sparkfun/SparkFun_Particulate_Matter_Sensor_Breakout_BMV080/docs/assets/img/BMV080_Breakout_Board_Secure.jpg

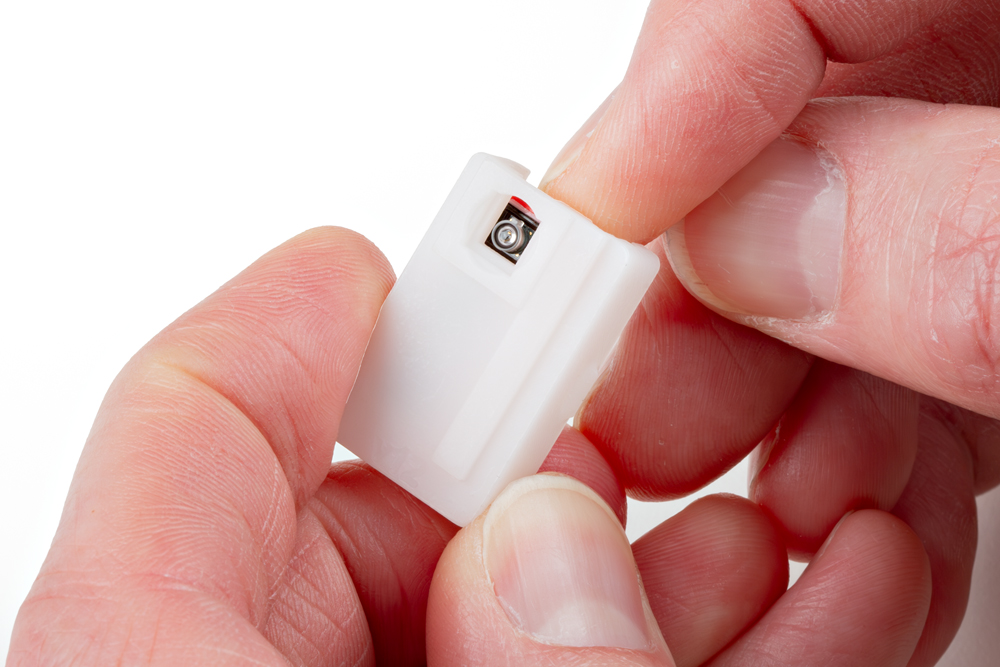
docs/assets/img/BMV080_Breakout_Board_Secure.jpg
