sparkfun/SparkFun_Particulate_Matter_Sensor_Breakout_BMV080/Enclosure/Demo_Mounting_Board/ESP32_ThingPlus_C_Dimensional_Mounting_001 (Meshed).stl

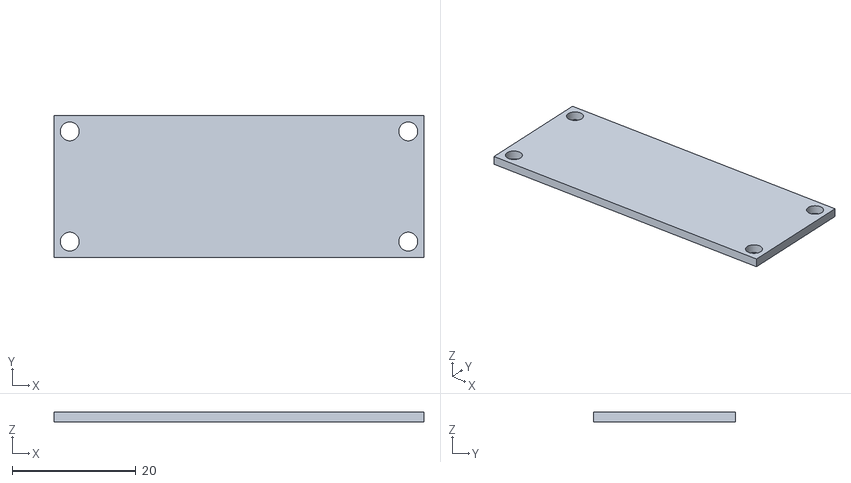
[picture p25: CAD file, 2024-12-12]
Enclosure/Demo_Mounting_Board/ESP32_ThingPlus_C_Dimensional_Mounting_001 (Meshed).stl
59.7 x 22.9 x 1.60
