sparkfun/SparkFun_Particulate_Matter_Sensor_Breakout_BMV080/Enclosure/Demo_Mounting_Board/HMV080_Demo_Mounting_Board_v02.dxf

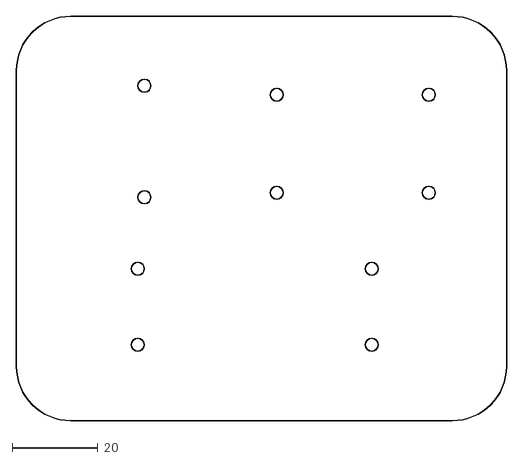
[picture p26: CAD file, 2024-12-11]
Enclosure/Demo_Mounting_Board/HMV080_Demo_Mounting_Board_v02.dxf
114.6 x 94.5
