sparkfun/SparkFun_Particulate_Matter_Sensor_Breakout_BMV080/Enclosure/Enclosure_(FreeCAD)/version_text_cutter.FCStd

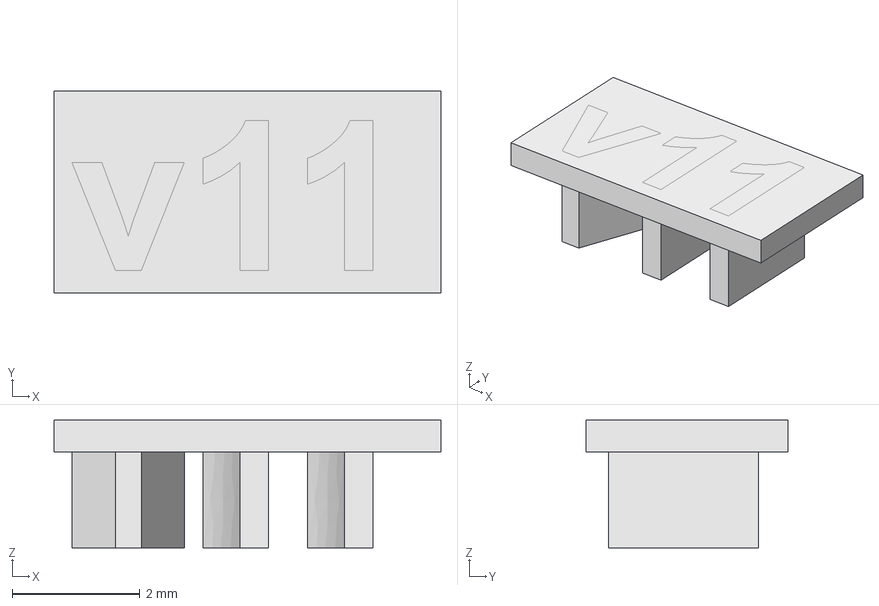
[picture p27: CAD file, 2025-02-10]
Enclosure/Enclosure_(FreeCAD)/version_text_cutter.FCStd
6.06 x 3.17 x 2.00 mm
