sparkfun/SparkFun_Particulate_Matter_Sensor_Breakout_BMV080/Enclosure/Enclosure_(FreeCAD)/PTH_Male_Header_Pin_01x01.FCStd

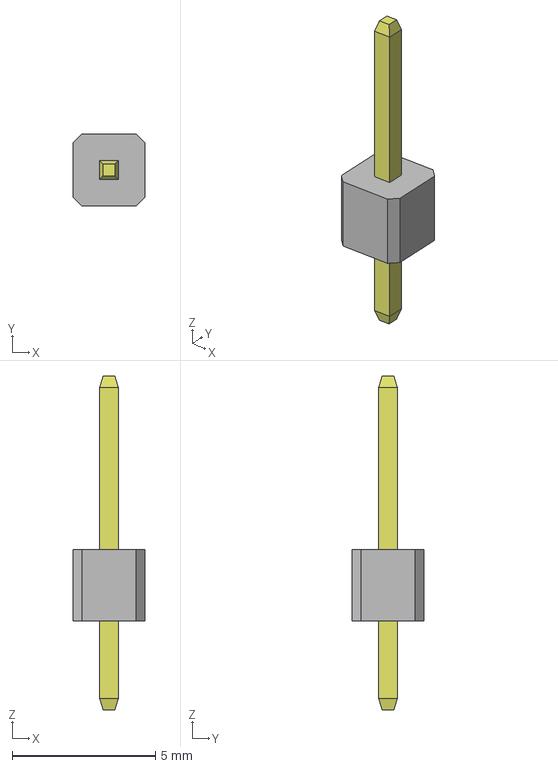
[picture p28: CAD file, 2025-02-04]
Enclosure/Enclosure_(FreeCAD)/PTH_Male_Header_Pin_01x01.FCStd
2.50 x 2.50 x 11.6 mm
Pin
Moulding
