sparkfun/SparkFun_Particulate_Matter_Sensor_Breakout_BMV080/Enclosure/Enclosure_(FreeCAD)/OS_Qwiic_Opening_cutaway.FCStd

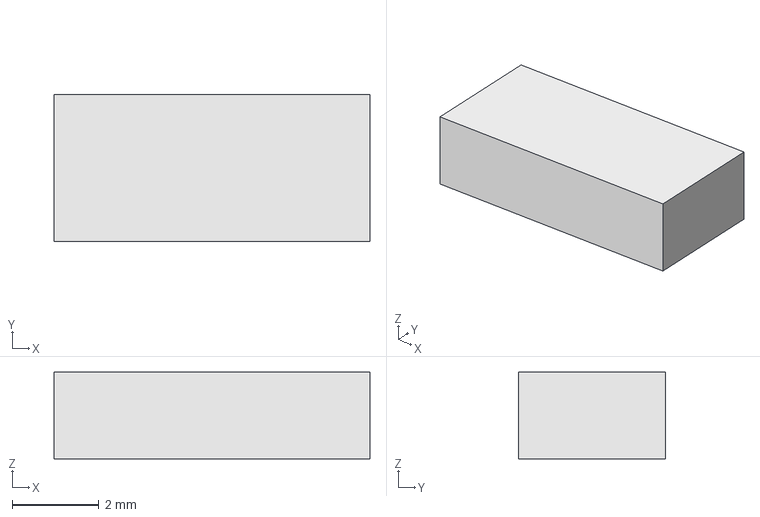
[picture p29: CAD file, 2025-02-04]
Enclosure/Enclosure_(FreeCAD)/OS_Qwiic_Opening_cutaway.FCStd
7.30 x 3.40 x 2.00 mm
