sparkfun/SparkFun_Particulate_Matter_Sensor_Breakout_BMV080/Enclosure/Enclosure_(FreeCAD)/PTH_Male_Header_Pin_01x07.FCStd

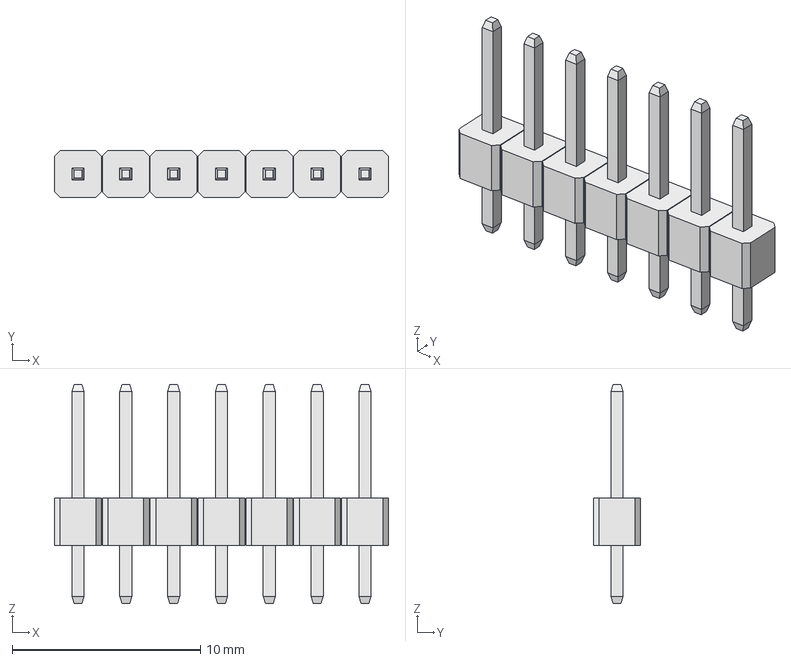
[picture p30: CAD file, 2025-02-04]
Enclosure/Enclosure_(FreeCAD)/PTH_Male_Header_Pin_01x07.FCStd
17.7 x 2.50 x 11.6 mm
