sparkfun/SparkFun_Particulate_Matter_Sensor_Breakout_BMV080/Enclosure/Enclosure_(FreeCAD)/sfe_flame_15mm.FCStd

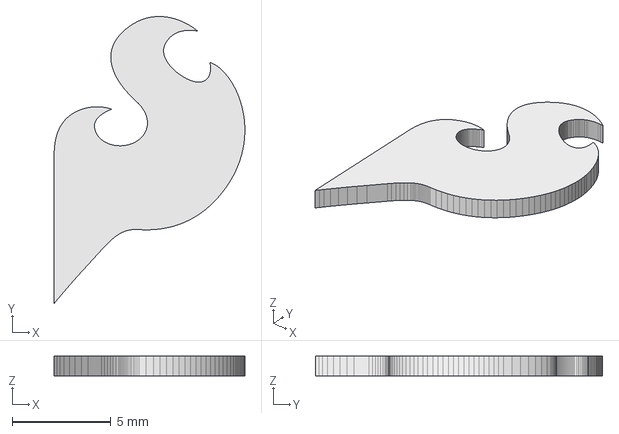
[picture p31: CAD file, 2025-02-04]
Enclosure/Enclosure_(FreeCAD)/sfe_flame_15mm.FCStd
9.67 x 14.5 x 1.00 mm
