sparkfun/SparkFun_Particulate_Matter_Sensor_Breakout_BMV080/Enclosure/Enclosure_(FreeCAD)/snap-fit_pin.FCStd

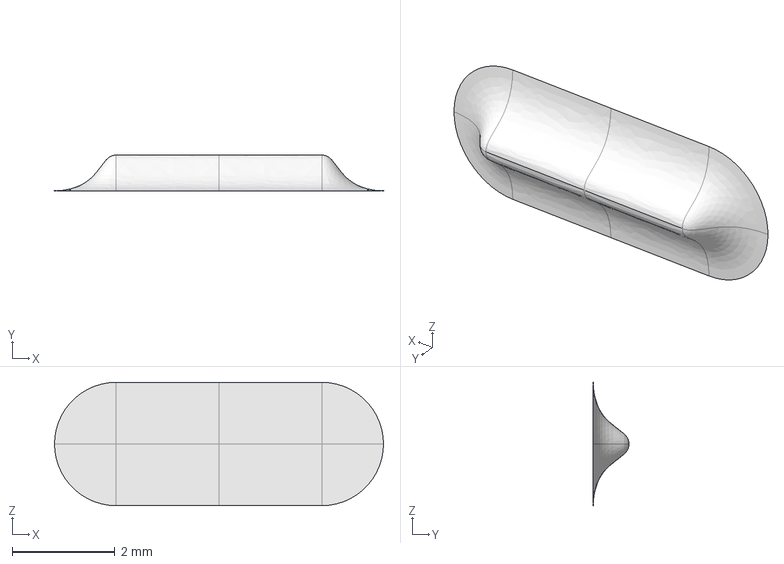
[picture p32: CAD file, 2025-02-04]
Enclosure/Enclosure_(FreeCAD)/snap-fit_pin.FCStd
6.40 x 0.7 x 2.40 mm
