sparkfun/SparkFun_Particulate_Matter_Sensor_Breakout_BMV080/Enclosure/Enclosure_(FreeCAD)/HMV080_Mounting_Flange.FCStd

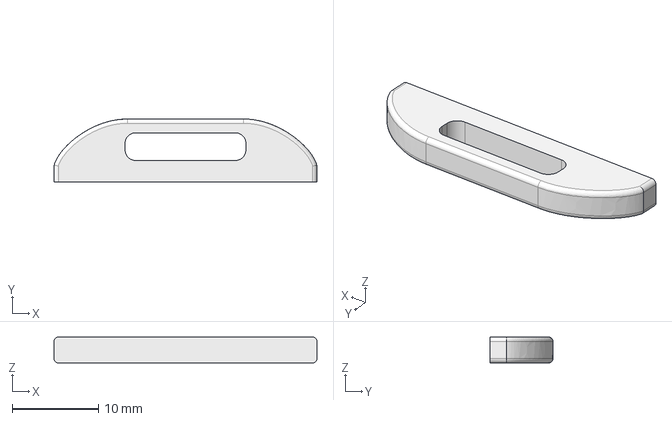
[picture p33: CAD file, 2025-02-04]
Enclosure/Enclosure_(FreeCAD)/HMV080_Mounting_Flange.FCStd
30.5 x 7.30 x 3.00 mm
