sparkfun/SparkFun_Particulate_Matter_Sensor_Breakout_BMV080/Enclosure/Enclosure_(FreeCAD)/snap-fit_pin-hole.FCStd

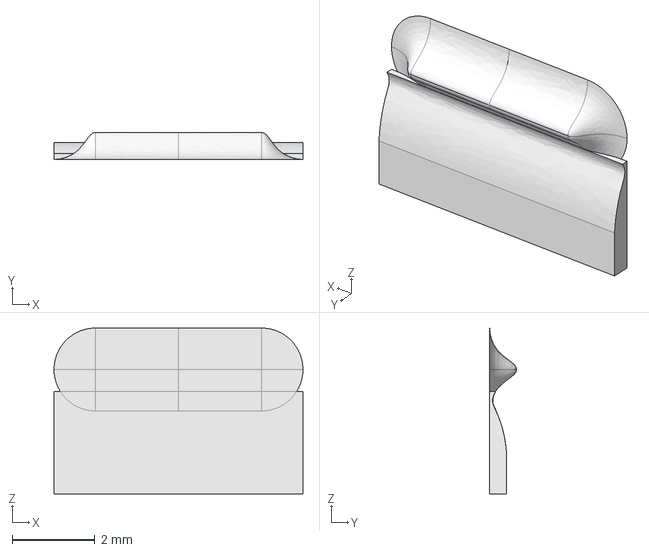
[picture p34: CAD file, 2025-02-04]
Enclosure/Enclosure_(FreeCAD)/snap-fit_pin-hole.FCStd
6.00 x 0.65 x 4.00 mm
