sparkfun/SparkFun_Particulate_Matter_Sensor_Breakout_BMV080/Enclosure/Enclosure_(FreeCAD)/HMV080_Optical_Cover_5x5x0.7mm.FCStd

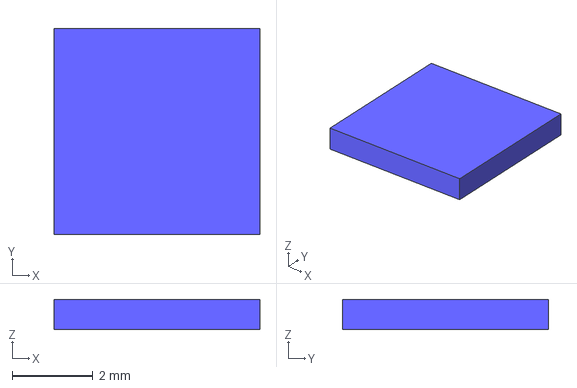
[picture p35: CAD file, 2024-11-26]
Enclosure/Enclosure_(FreeCAD)/HMV080_Optical_Cover_5x5x0.7mm.FCStd
5.10 x 5.10 x 0.75 mm
