sparkfun/SparkFun_Particulate_Matter_Sensor_Breakout_BMV080/Enclosure/Enclosure_(FreeCAD)/BMV080_Sensor_and_FPC_Connector.step

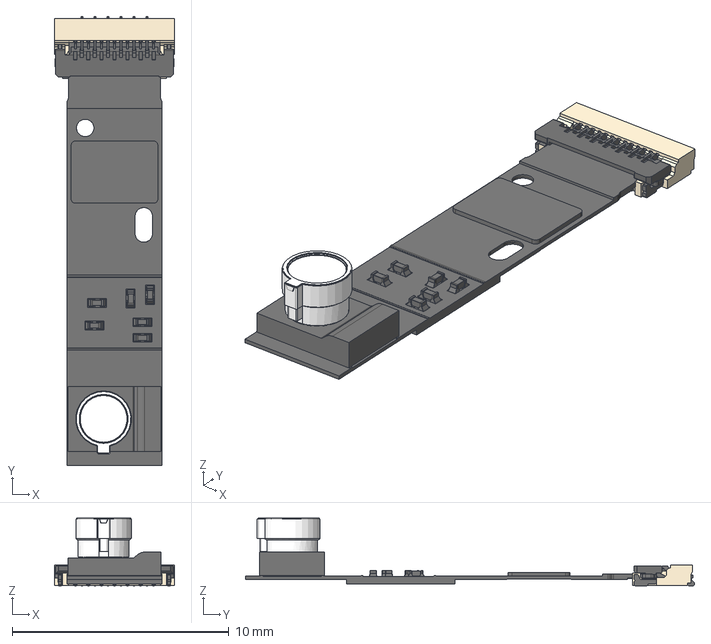
[picture p36: CAD file, 2024-11-15]
Enclosure/Enclosure_(FreeCAD)/BMV080_Sensor_and_FPC_Connector.step
5.55 x 20.7 x 3.11 mm
BMV080_simplified v2
Molex_5035661302 v1
