sparkfun/SparkFun_Particulate_Matter_Sensor_Breakout_BMV080/Enclosure/Enclosure_(FreeCAD)/FPC_0.3mm-13_MOLEX_503566-1302.step

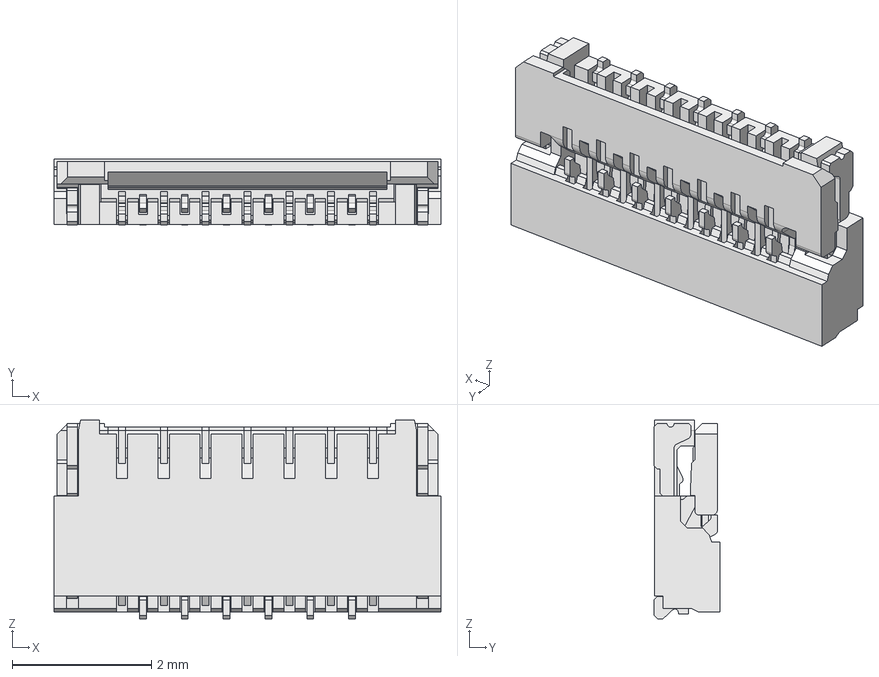
[picture p37: CAD file, 2024-08-16]
Enclosure/Enclosure_(FreeCAD)/FPC_0.3mm-13_MOLEX_503566-1302.step
5.55 x 0.95 x 2.85 mm
